blackmountaindesign/LightMeter/Assemblies/Battery_Holder_Assembly/bat1.JPG

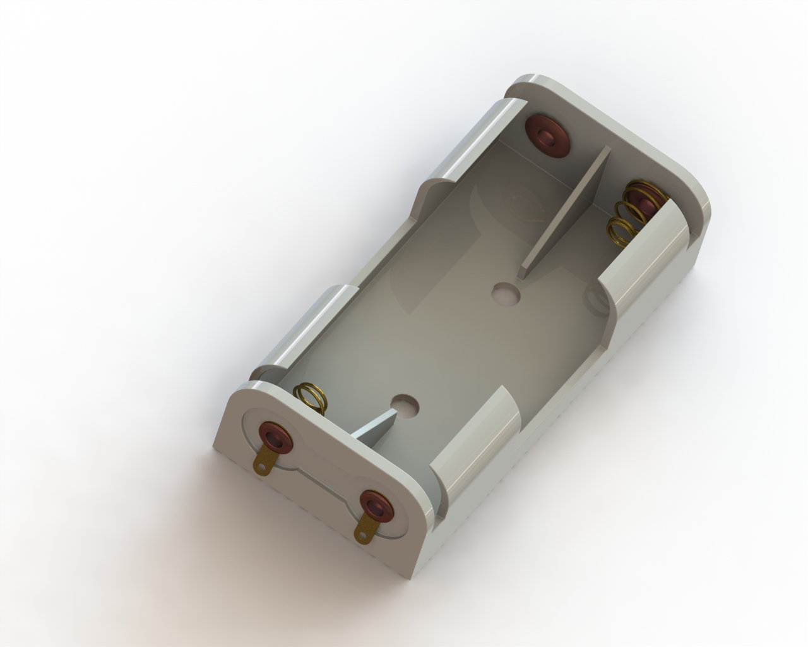
Assemblies/Battery_Holder_Assembly/bat1.JPG
