blackmountaindesign/LightMeter/Assemblies/Battery_Holder_Assembly/bat2.JPG

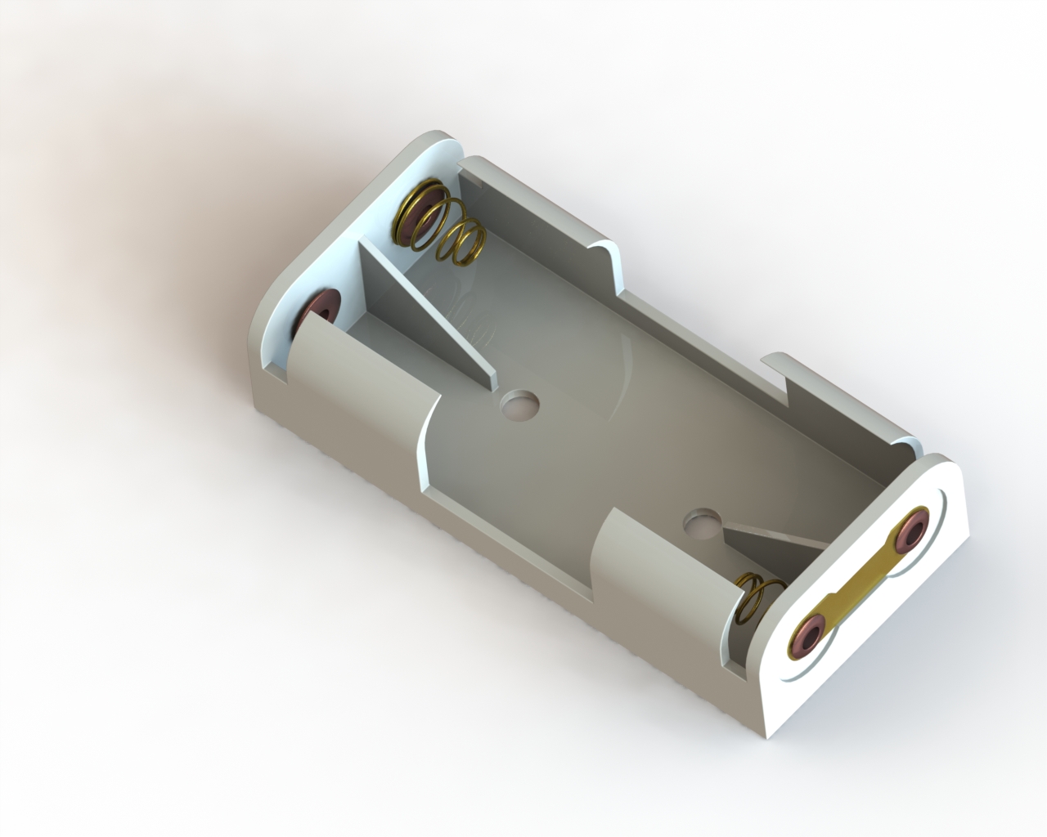
Assemblies/Battery_Holder_Assembly/bat2.JPG
