blackmountaindesign/LightMeter/Assemblies/Prototyping_Board_Part/PrototypingBreadboard_4x6cm.jpg

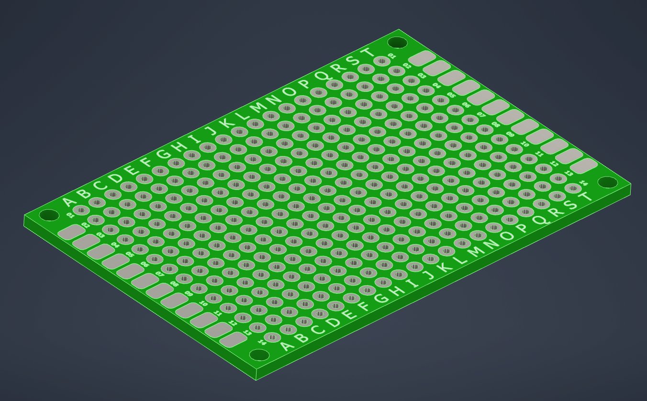
Assemblies/Prototyping_Board_Part/PrototypingBreadboard_4x6cm.jpg
