blackmountaindesign/LightMeter/Assemblies/Prototyping_Board_Part/PrototypingBreadboard_5x7cm.jpg

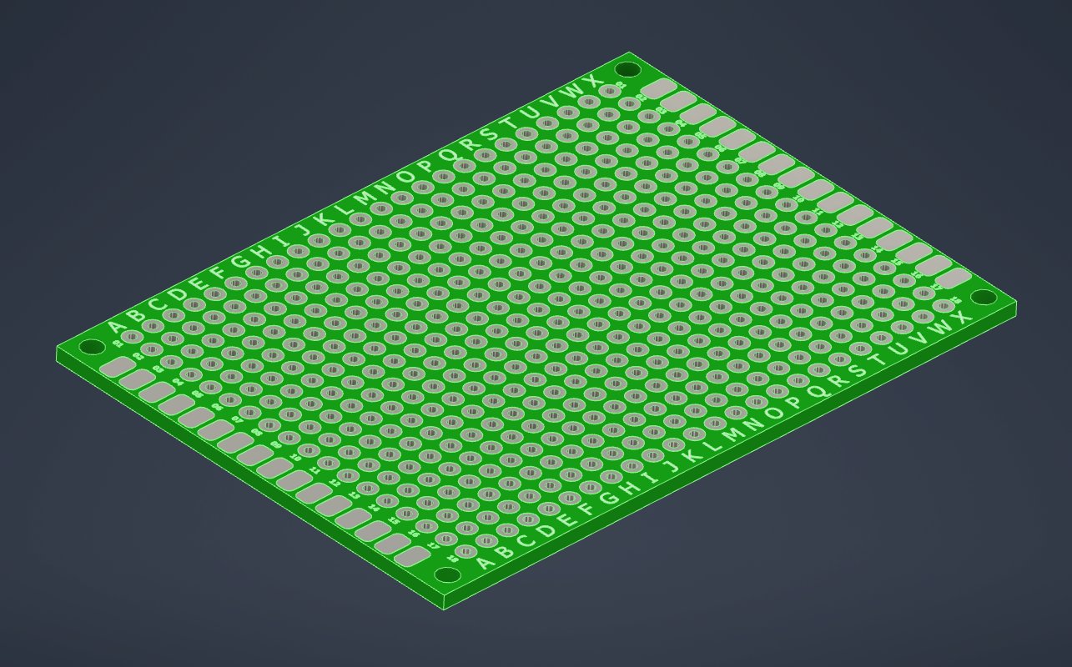
Assemblies/Prototyping_Board_Part/PrototypingBreadboard_5x7cm.jpg
