blackmountaindesign/LightMeter/Assemblies/pushbutton-red-1.snapshot.3/Button_red_S2.png

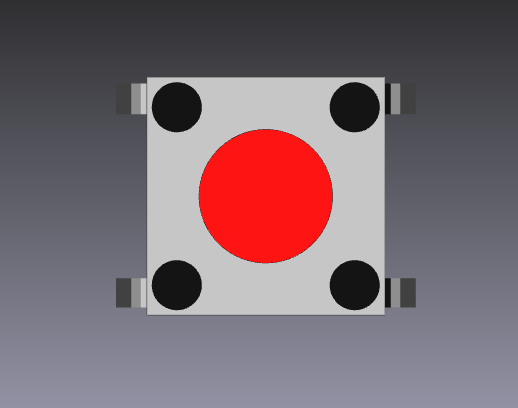
Assemblies/pushbutton-red-1.snapshot.3/Button_red_S2.png
