blackmountaindesign/LightMeter/Assemblies/pushbutton-red-1.snapshot.3/Button_red_s3.png

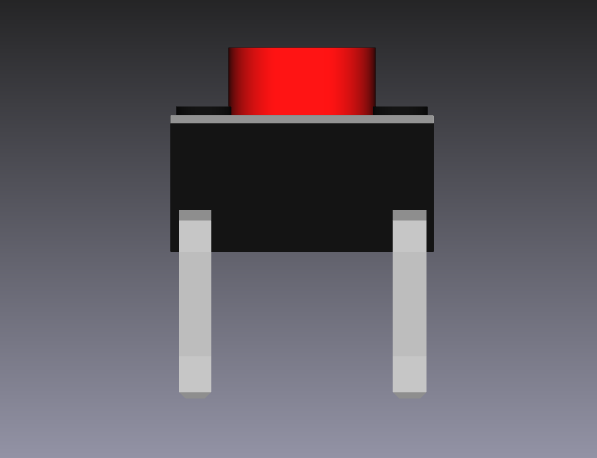
Assemblies/pushbutton-red-1.snapshot.3/Button_red_s3.png
